jrleeman/3DCompass/Fritzing/3D_Compass_schem.png

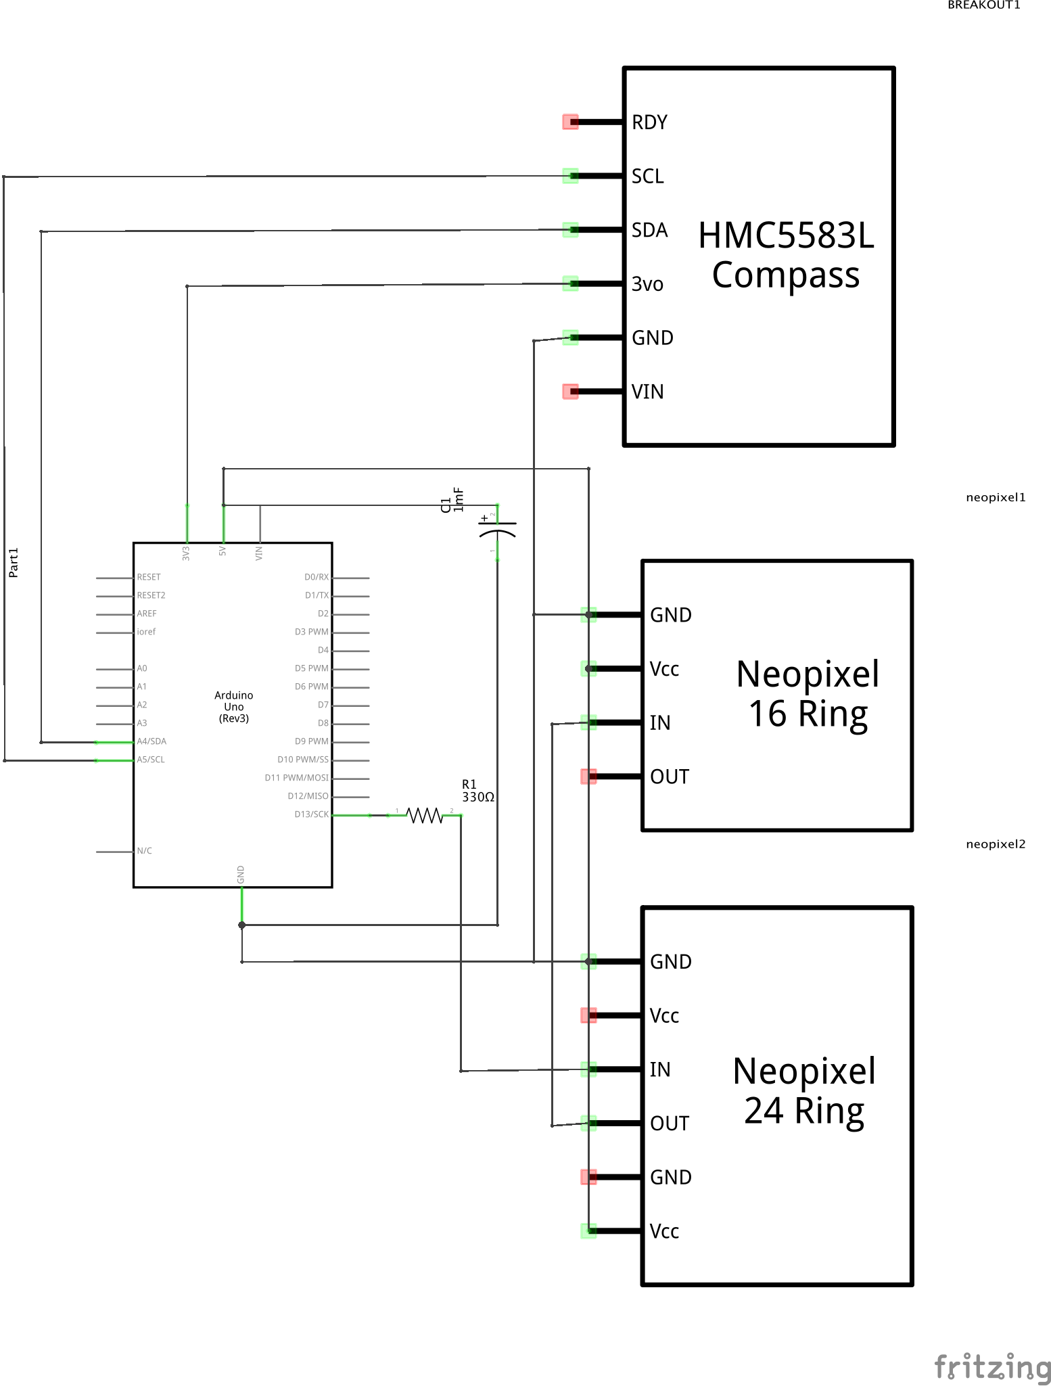
Fritzing/3D_Compass_schem.png
