jrleeman/3DCompass/Photos/coordinates.jpg

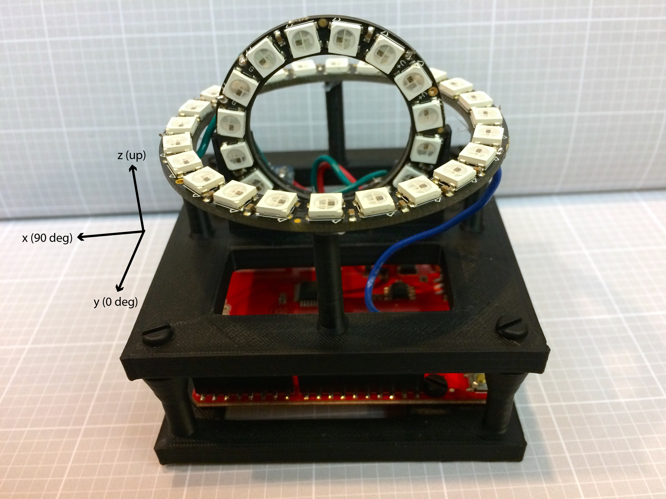
Photos/coordinates.jpg
