jrleeman/3DCompass/Photos/front.jpg

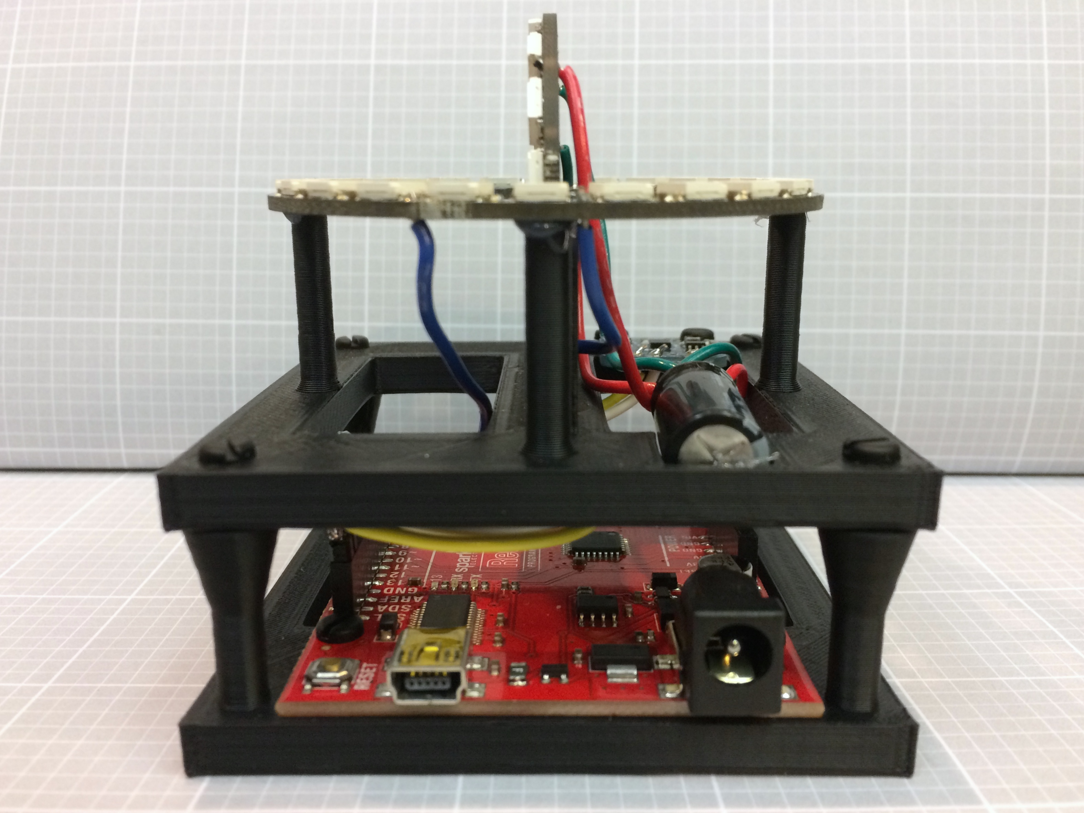
Photos/front.jpg
