jrleeman/3DCompass/Photos/top_detail.jpg

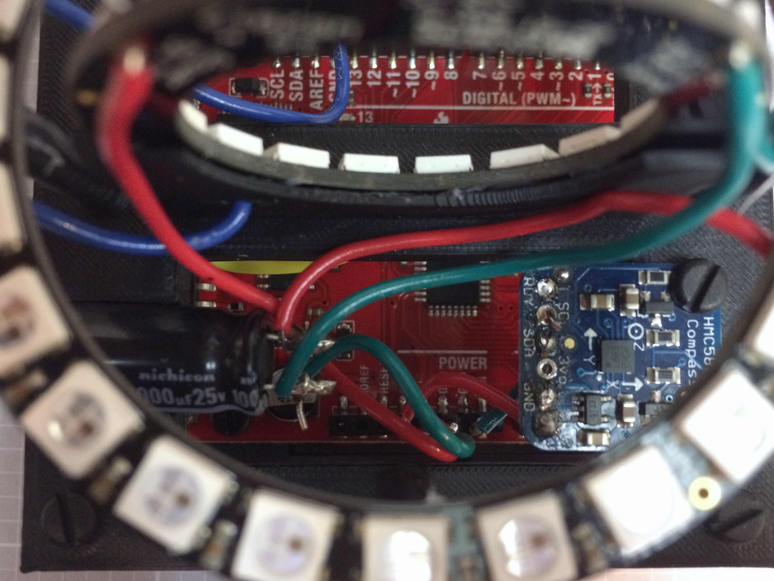
Photos/top_detail.jpg
